uwrov/nanofloat/NanoBoard/NB002/NB002.png

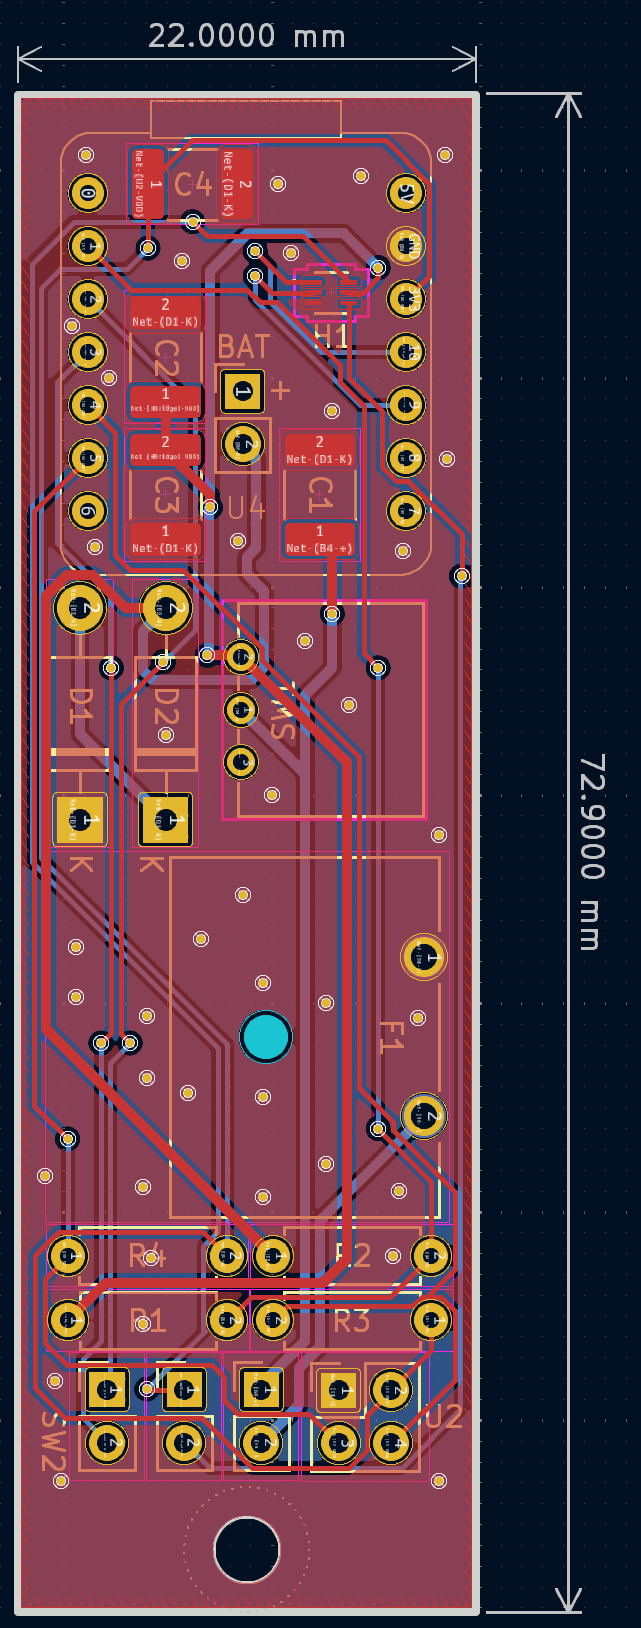
NanoBoard/NB002/NB002.png
