uwrov/nanofloat/NanoBoard/NB102/NB102-TEMP.png

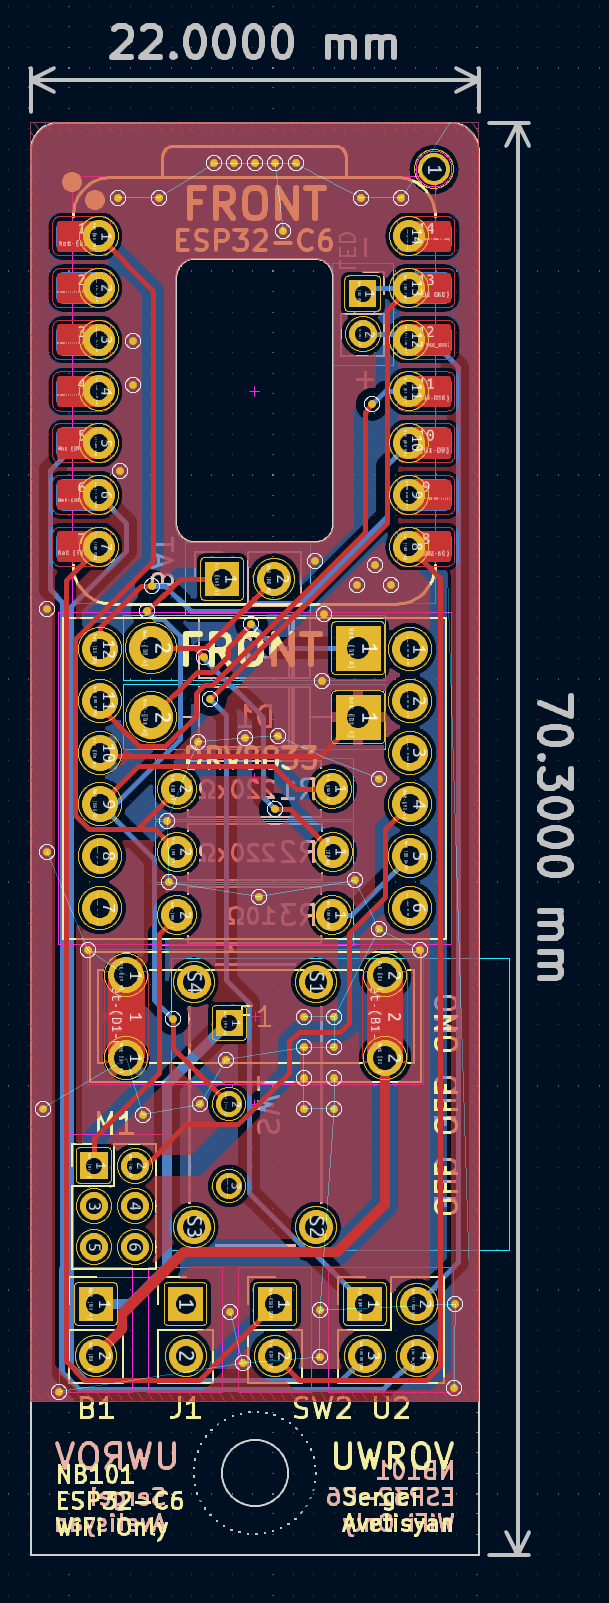
NanoBoard/NB102/NB102-TEMP.png
